Raphael-Leb/Arduino-Macro-Pad/MainPad/Models/pec11r-4220k_l13-8_w12-4_h26-5.stp

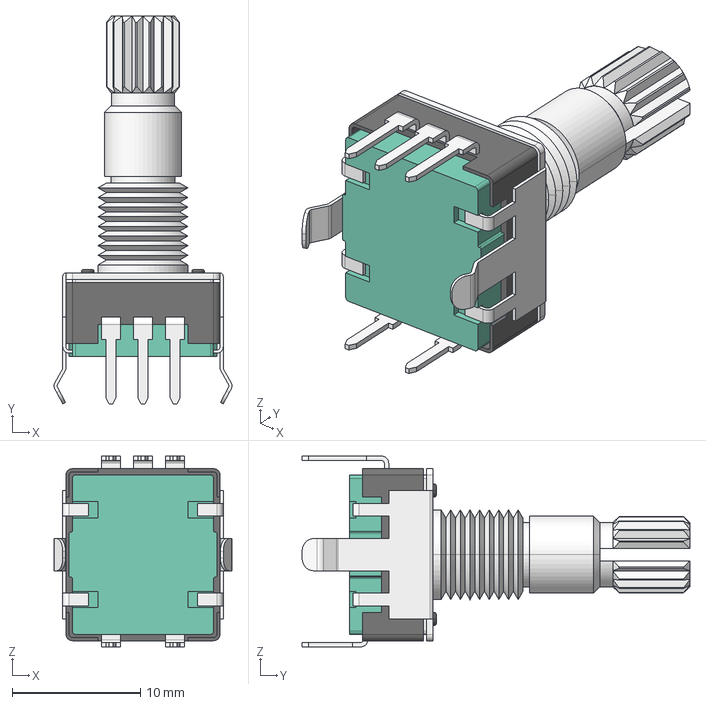
[picture p10: CAD file, 2023-09-17]
MainPad/Models/pec11r-4220k_l13-8_w12-4_h26-5.stp
13.9 x 30.2 x 14.8 mm
