Raphael-Leb/Arduino-Macro-Pad/MainPad/PCBfiles/MainPad.kicad_sch

## KiCad design MainPad/PCBfiles/MainPad.kicad_sch (2023-09-17)

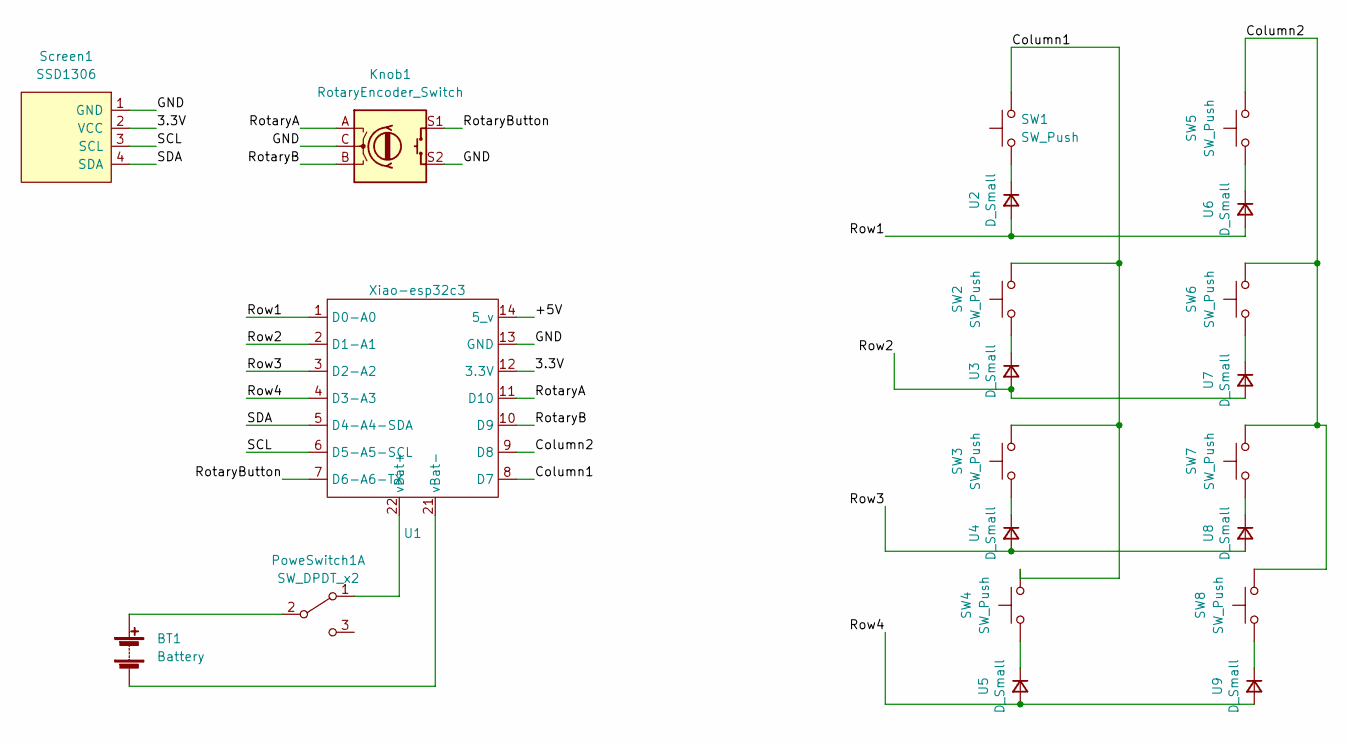
[picture p11: schematic MainPad.kicad_sch]

Parts:
BT1: Battery; Battery_Panasonic_CR1025-VSK_Vertical_CircularHoles
Knob1: RotaryEncoder_Switch; RotaryEncoder_Alps_EC11E-Switch_Vertical_H20mm
PoweSwitch1: SW_DPDT_x2; SLIDE-SWITCH
SW1, SW2, SW3, SW4, SW5, SW6, SW7, SW8: SW_Push; SW_Cherry_MX_1.00u_PCB
Screen1: SSD1306; 128x64OLED
U1: Xiao-esp32c3; Seeeduino_XIAO-MOUDLE14P-2.54-21X17.8MM
U2, U3, U4, U5, U6, U7, U8, U9: D_Small; D_DO-35_SOD27_P7.62mm_Horizontal

Connections:
3.3V: Screen1.2 (VCC), U1.12 (3.3V)
+5V: U1.14 (5_v)
Column1: SW1.2, SW2.2, SW3.2, SW4.2, U1.8 (D7)
Column2: SW5.2, SW6.2, SW7.2, SW8.2, U1.9 (D8)
GND: Knob1.C, Knob1.S2, Screen1.1 (GND), U1.13 (GND)
unnamed: BT1.1 (+), PoweSwitch1.2 (B)
unnamed: BT1.2 (-), U1.21 (vBat-)
unnamed: PoweSwitch1.1 (A), U1.22 (vBat+)
unnamed: SW1.1, U2.1 (K)
unnamed: SW2.1, U3.1 (K)
unnamed: SW3.1, U4.1 (K)
unnamed: SW4.1, U5.1 (K)
unnamed: SW5.1, U6.1 (K)
unnamed: SW6.1, U7.1 (K)
unnamed: SW7.1, U8.1 (K)
unnamed: SW8.1, U9.1 (K)
RotaryA: Knob1.A, U1.11 (D10)
RotaryB: Knob1.B, U1.10 (D9)
RotaryButton: Knob1.S1, U1.7 (D6-A6-TX)
Row1: U1.1 (D0-A0), U2.2 (A), U6.2 (A)
Row2: U1.2 (D1-A1), U3.2 (A), U7.2 (A)
Row3: U1.3 (D2-A2), U4.2 (A), U8.2 (A)
Row4: U1.4 (D3-A3), U5.2 (A), U9.2 (A)
SCL: Screen1.3 (SCL), U1.6 (D5-A5-SCL)
SDA: Screen1.4 (SDA), U1.5 (D4-A4-SDA)
